ericmcdaniel/lumenlab/board/images/lumenlab-mounting-bracket-2.png

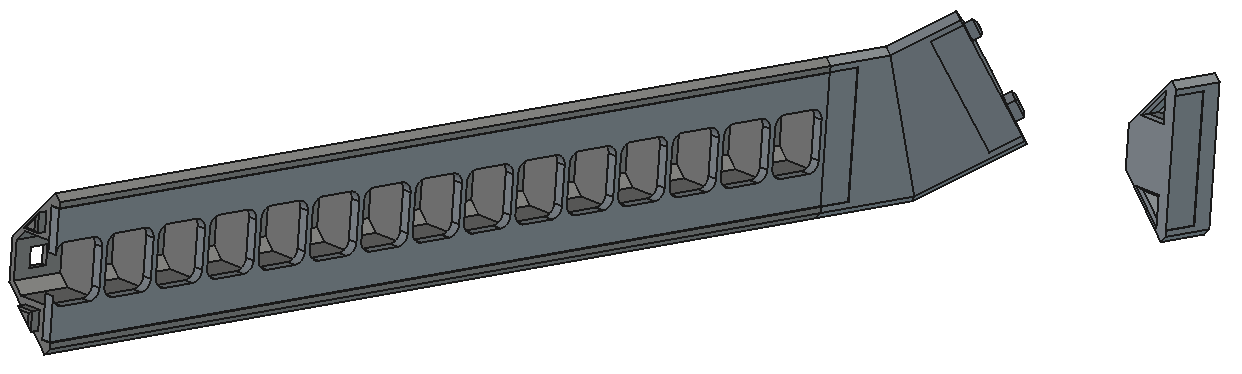
board/images/lumenlab-mounting-bracket-2.png
