ericmcdaniel/lumenlab/board/3d-models/0ZRE0005FF1C.stp

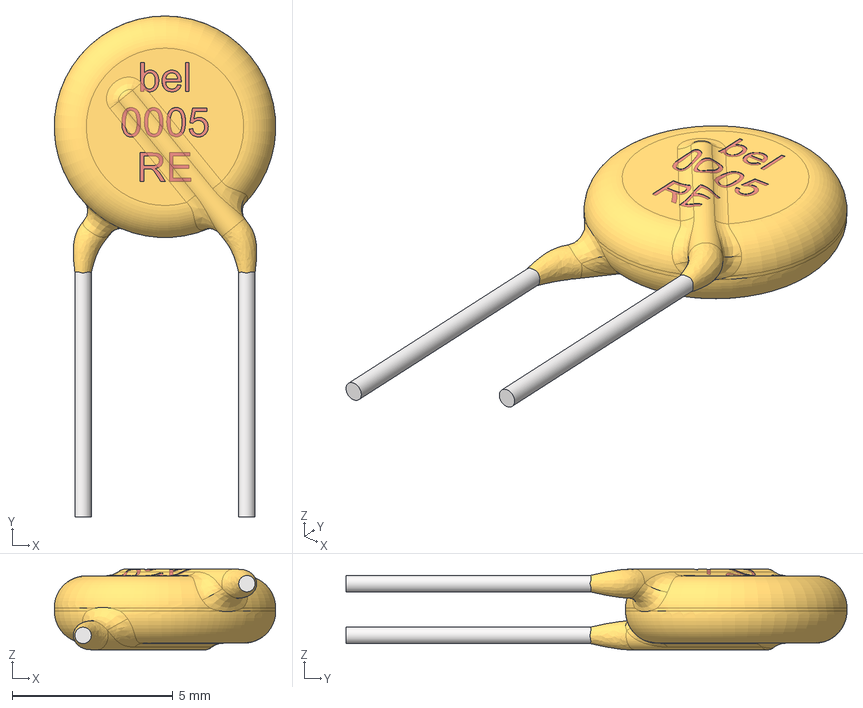
[picture p35: CAD file, 2025-10-11]
board/3d-models/0ZRE0005FF1C.stp
6.90 x 15.6 x 2.52 mm
0ZRE0005FF1C_PART1
0ZRE0005FF1C_PART2
0ZRE0005FF1C_PART3
0ZRE0005FF1C_PART4
