ericmcdaniel/lumenlab/board/mount/v3/led-strip-v3-bracket-only-mounting-guide.3mf

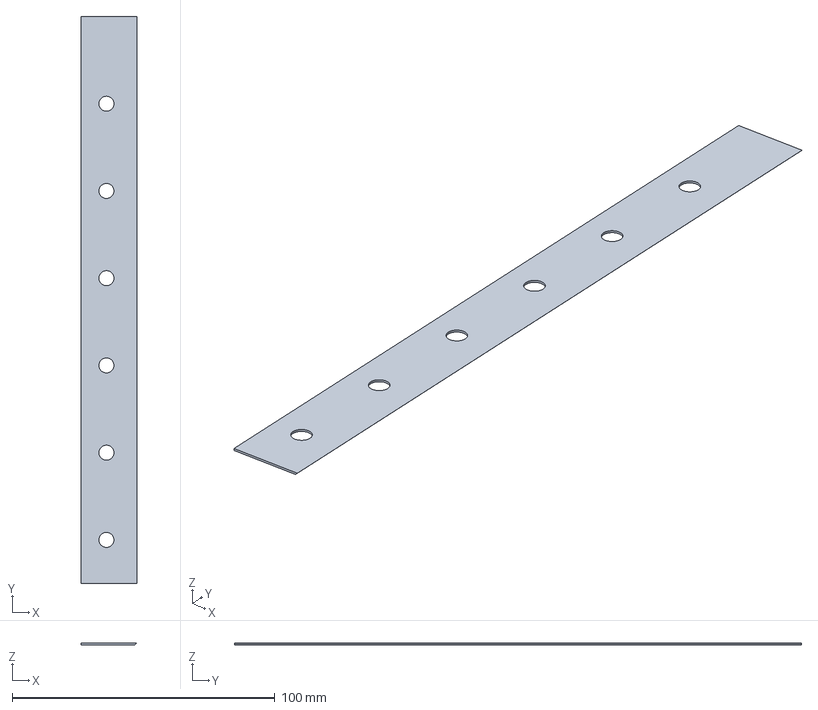
[picture p36: CAD file, 2026-06-20]
board/mount/v3/led-strip-v3-bracket-only-mounting-guide.3mf
21.1 x 215.7 x 0.604 mm
