ericmcdaniel/lumenlab/board/3d-models/CP2102N-A02-GQFN24R.step

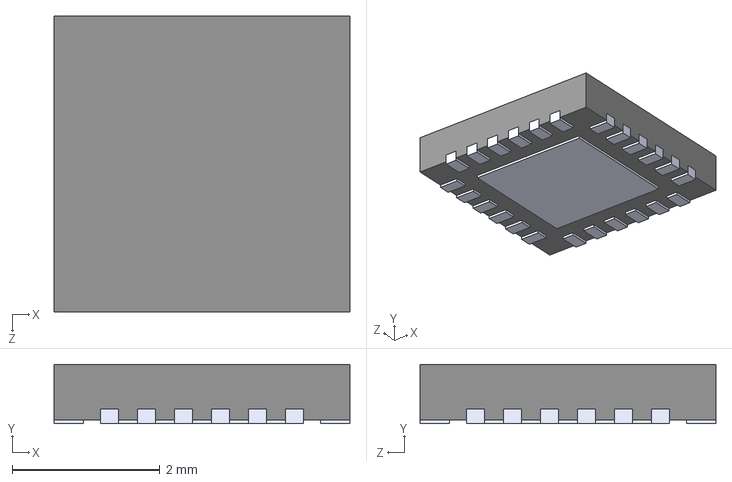
[picture p37: CAD file, 2025-10-11]
board/3d-models/CP2102N-A02-GQFN24R.step
4.00 x 0.8 x 4.00 mm
