ericmcdaniel/lumenlab/board/3d-models/ESD122DMYR.step

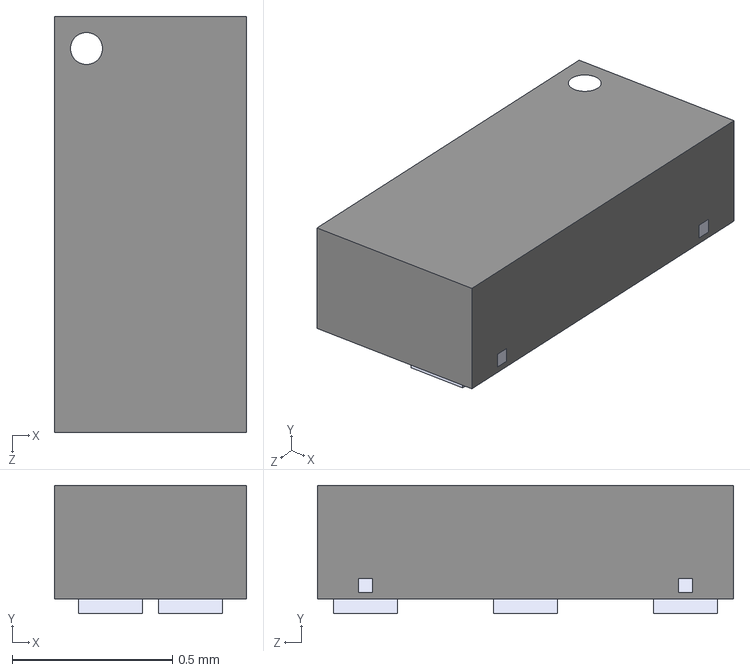
[picture p38: CAD file, 2025-10-11]
board/3d-models/ESD122DMYR.step
0.6 x 0.4 x 1.30 mm
