ericmcdaniel/lumenlab/board/mount/v3/plywood-retention-clip.3mf

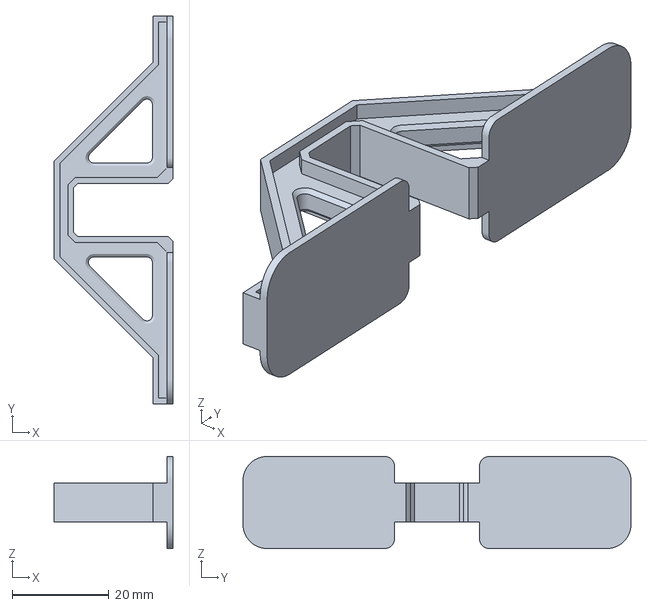
[picture p39: CAD file, 2026-05-21]
board/mount/v3/plywood-retention-clip.3mf
24.5 x 80.0 x 19.0 mm
