ericmcdaniel/lumenlab/board/3d-models/B4PS-VH-jst-vh-connector.step

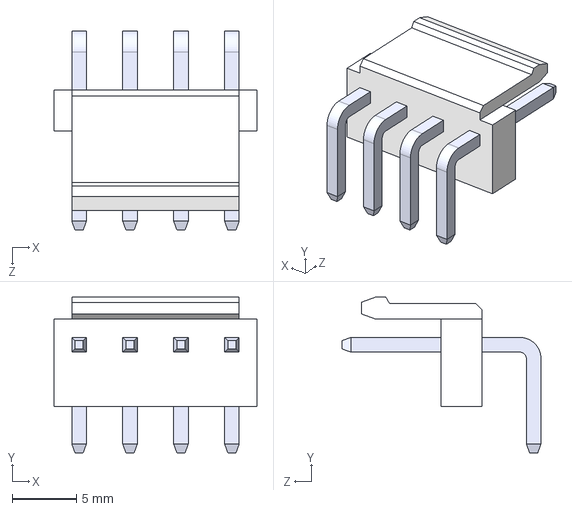
[picture p40: CAD file, 2025-10-11]
board/3d-models/B4PS-VH-jst-vh-connector.step
15.8 x 12.1 x 15.5 mm
BxPS-VH_4
pin^BxPS-VH ass x 4
