ericmcdaniel/lumenlab/board/mount/v3/led-strip-v3-bracket-only.3mf

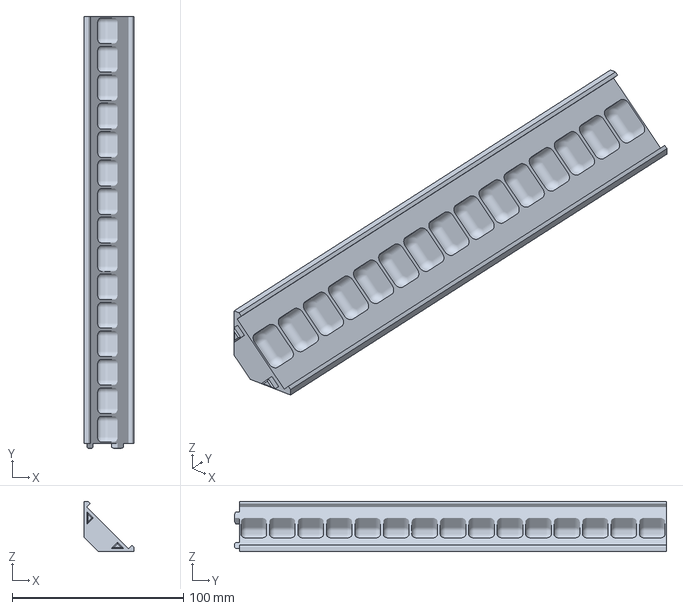
[picture p41: CAD file, 2026-04-02]
board/mount/v3/led-strip-v3-bracket-only.3mf
29.2 x 252.4 x 29.2 mm
