ericmcdaniel/lumenlab/board/3d-models/EMZS250ARA102MJA0G-led-decoupling-cap.step

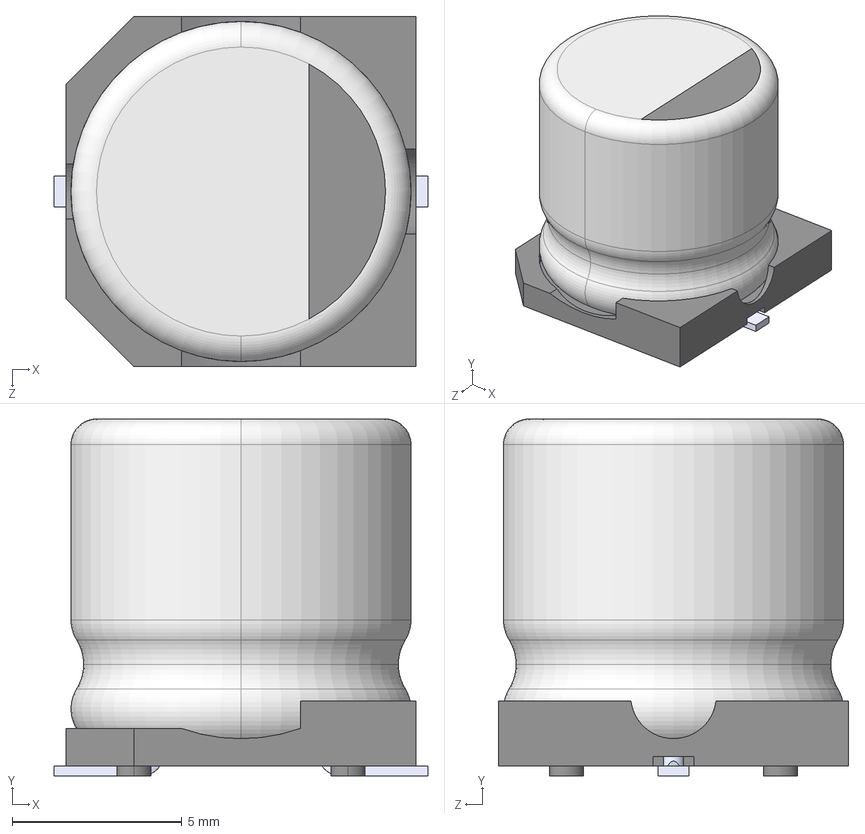
[picture p42: CAD file, 2025-10-11]
board/3d-models/EMZS250ARA102MJA0G-led-decoupling-cap.step
11.0 x 10.5 x 10.3 mm
