ericmcdaniel/lumenlab/board/mount/v3/led-strip-v3-bracket-mirrored.3mf

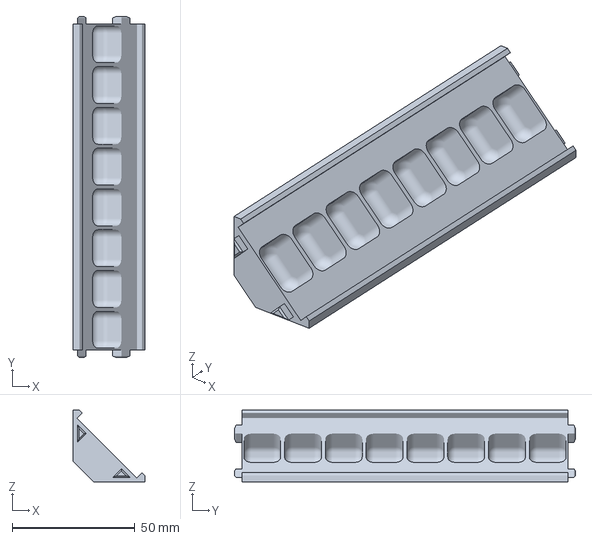
[picture p43: CAD file, 2026-04-02]
board/mount/v3/led-strip-v3-bracket-mirrored.3mf
29.2 x 139.0 x 29.2 mm
