ericmcdaniel/lumenlab/board/3d-models/USB-C.step

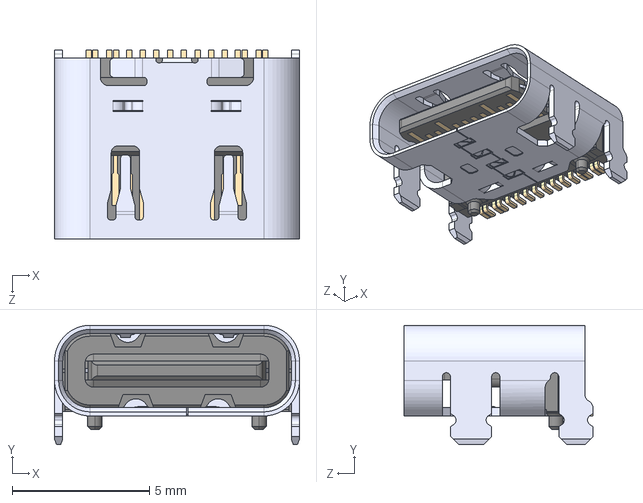
[picture p44: CAD file, 2025-10-11]
board/3d-models/USB-C.step
8.94 x 4.36 x 6.90 mm
