ericmcdaniel/lumenlab/board/mount/v3/led-strip-v3-bracket-w-endcap.3mf

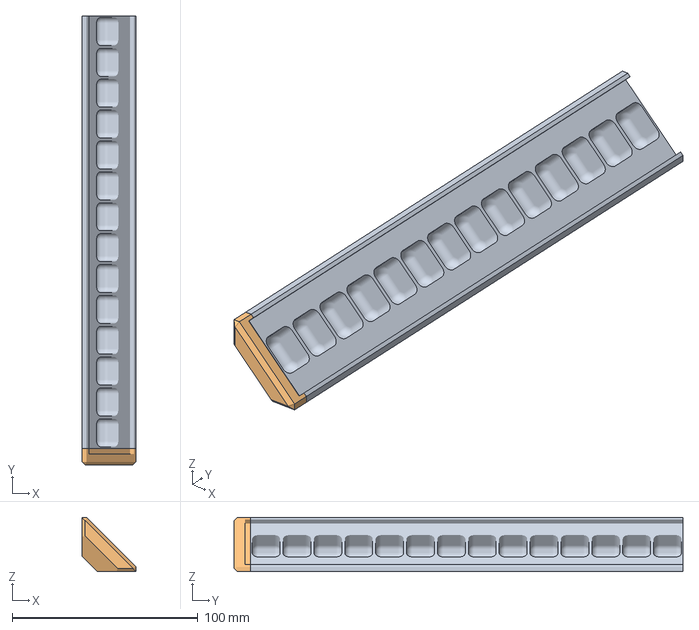
[picture p45: CAD file, 2026-04-02]
board/mount/v3/led-strip-v3-bracket-w-endcap.3mf
29.2 x 241.8 x 29.2 mm
