ericmcdaniel/lumenlab/board/3d-models/potentiometer.step

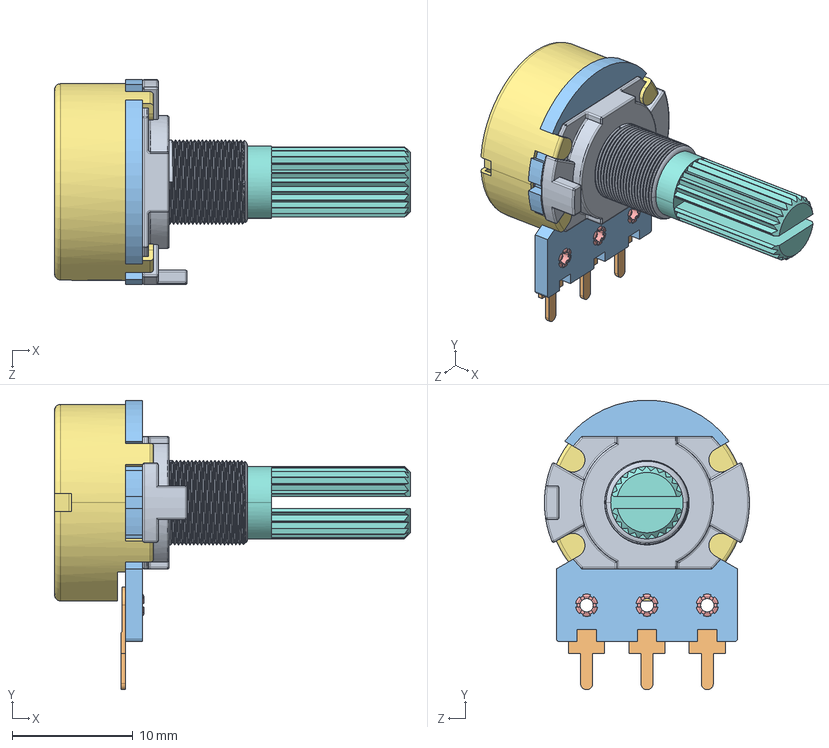
[picture p46: CAD file, 2025-10-01]
board/3d-models/potentiometer.step
29.5 x 24.0 x 17.0 mm
PTN16_1 BUSHING
PTN16-A_1 HOUSING
PTN16_20K1_SHAFT
