ericmcdaniel/lumenlab/board/mount/v3/led-strip-v3-bracket-w-45deg-joint.3mf

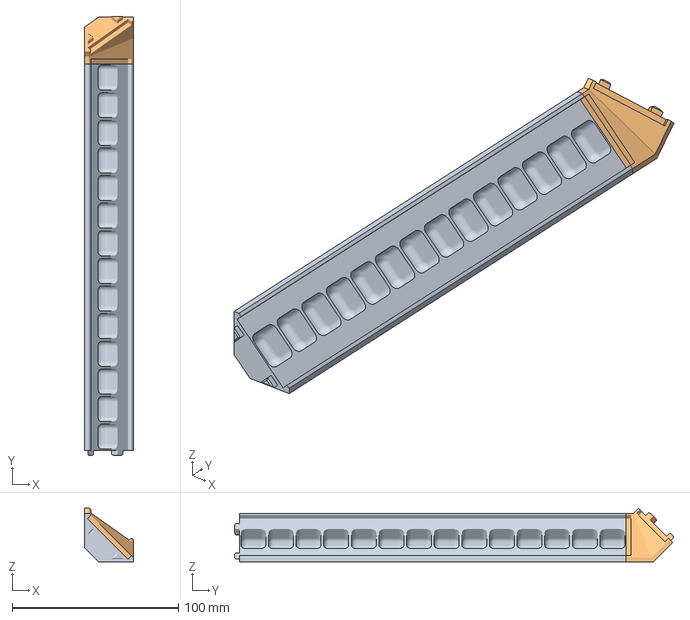
[picture p47: CAD file, 2026-04-02]
board/mount/v3/led-strip-v3-bracket-w-45deg-joint.3mf
29.3 x 264.3 x 32.3 mm
