ericmcdaniel/lumenlab/board/3d-models/BarrelJack.step

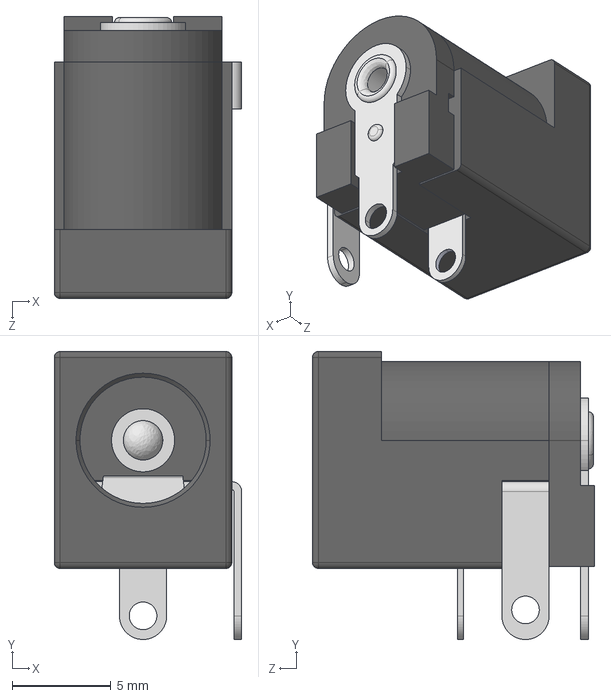
[picture p48: CAD file, 2025-10-01]
board/3d-models/BarrelJack.step
9.50 x 14.6 x 14.3 mm
