ericmcdaniel/lumenlab/board/3d-models/SSD1306.step

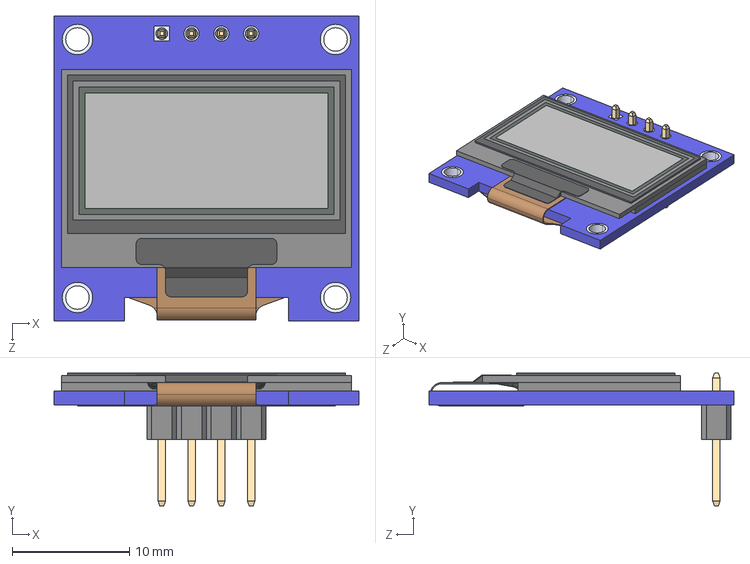
[picture p49: CAD file, 2025-10-01]
board/3d-models/SSD1306.step
26.0 x 11.3 x 26.0 mm
DM-OLED096-636_Module
DM-OLED096-636_Panel
