ericmcdaniel/lumenlab/board/3d-models/1264EY-6R8M_P3-inductor.step

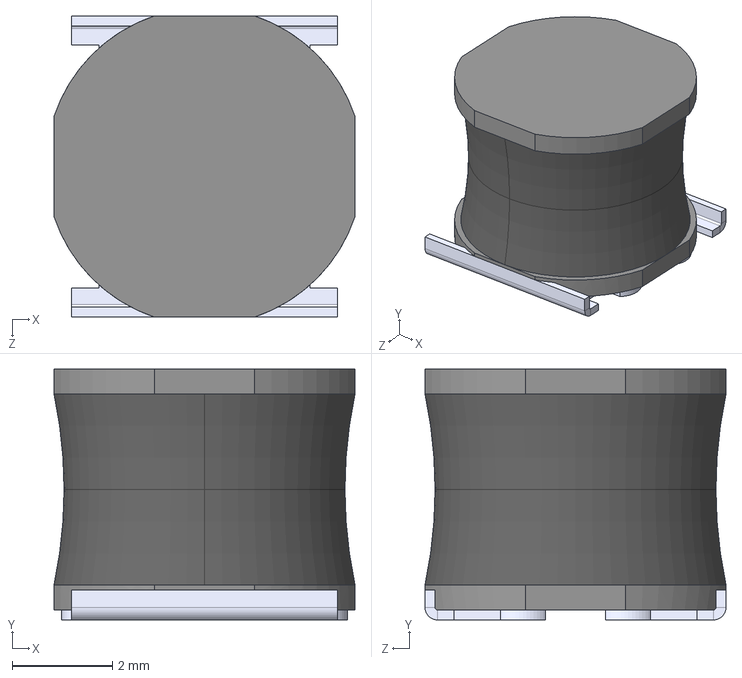
[picture p50: CAD file, 2025-10-01]
board/3d-models/1264EY-6R8M_P3-inductor.step
6.00 x 5.00 x 6.00 mm
