ericmcdaniel/lumenlab/board/3d-models/504-nav-switch.stp

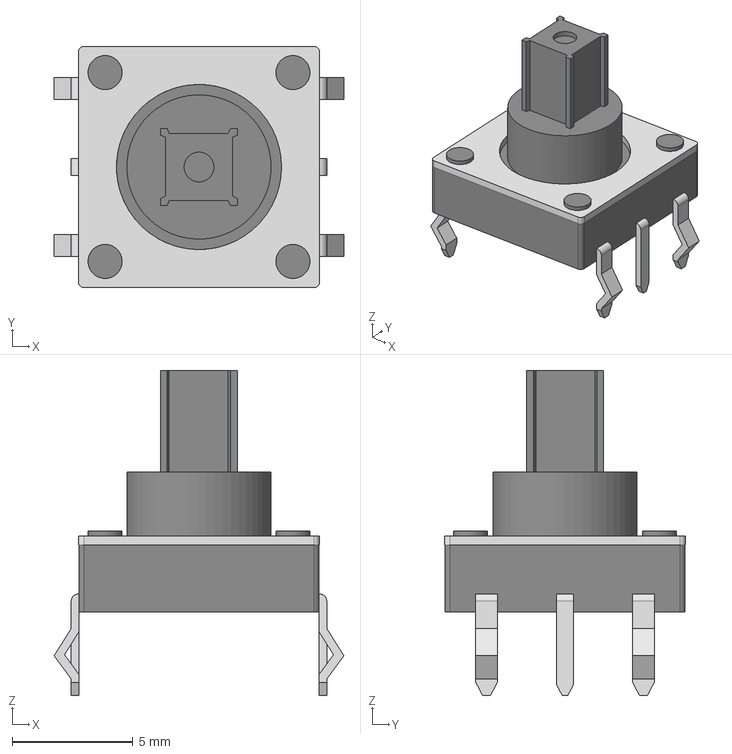
[picture p51: CAD file, 2025-10-01]
board/3d-models/504-nav-switch.stp
12.0 x 10.0 x 13.5 mm
