ericmcdaniel/lumenlab/board/3d-models/B2B-PH-K-S.step

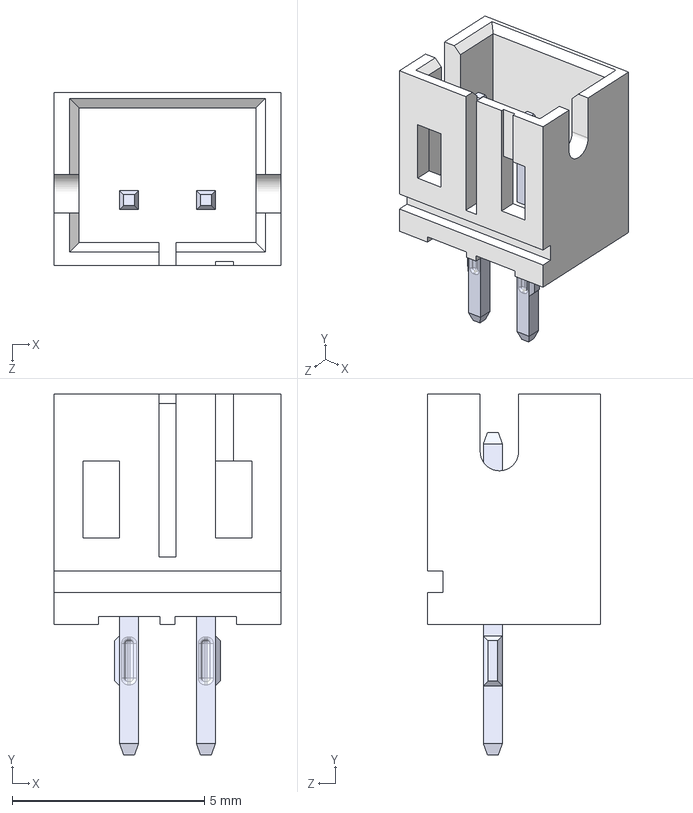
[picture p52: CAD file, 2025-10-01]
board/3d-models/B2B-PH-K-S.step
5.90 x 9.40 x 4.50 mm
