ericmcdaniel/lumenlab/board/3d-models/16SEPF1000M.step

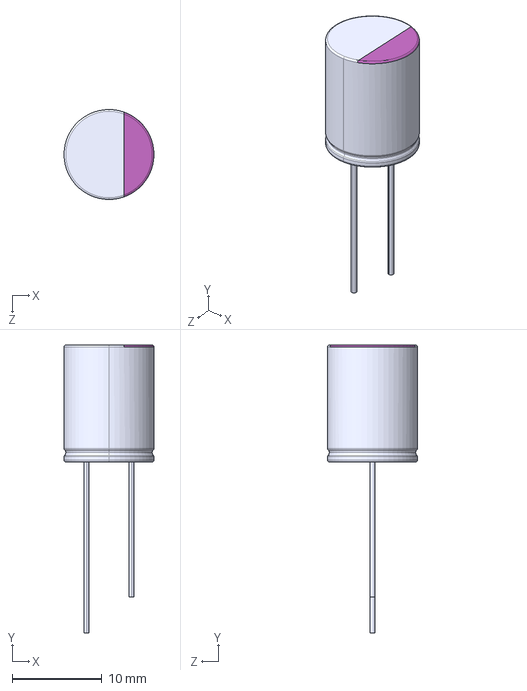
[picture p53: CAD file, 2025-10-01]
board/3d-models/16SEPF1000M.step
10.0 x 32.0 x 10.0 mm
