ericmcdaniel/lumenlab/board/3d-models/SMAJ12CA-tvs-diode.step

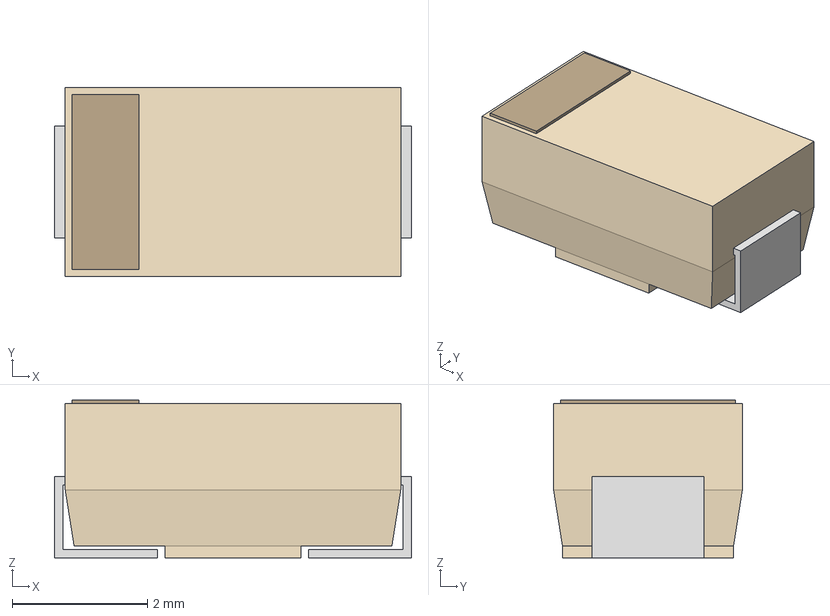
[picture p54: CAD file, 2025-10-01]
board/3d-models/SMAJ12CA-tvs-diode.step
5.28 x 2.79 x 2.34 mm
