ericmcdaniel/lumenlab/board/3d-models/10TZV220M6-speaker-cap.step

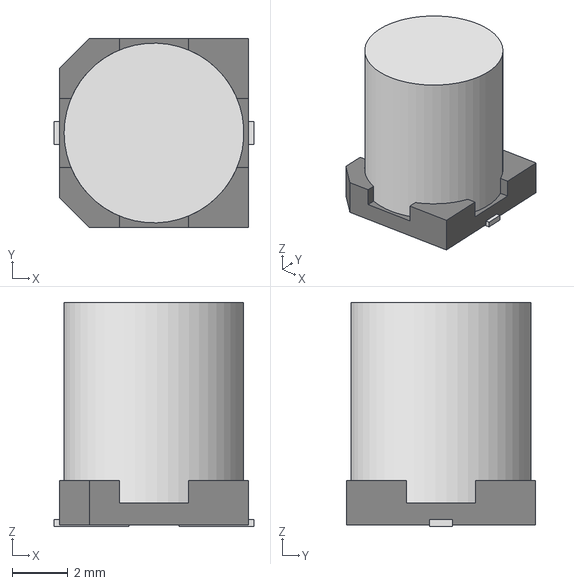
[picture p55: CAD file, 2025-10-01]
board/3d-models/10TZV220M6-speaker-cap.step
7.19 x 6.81 x 8.05 mm
