ericmcdaniel/lumenlab/board/3d-models/JTAG-header.STEP

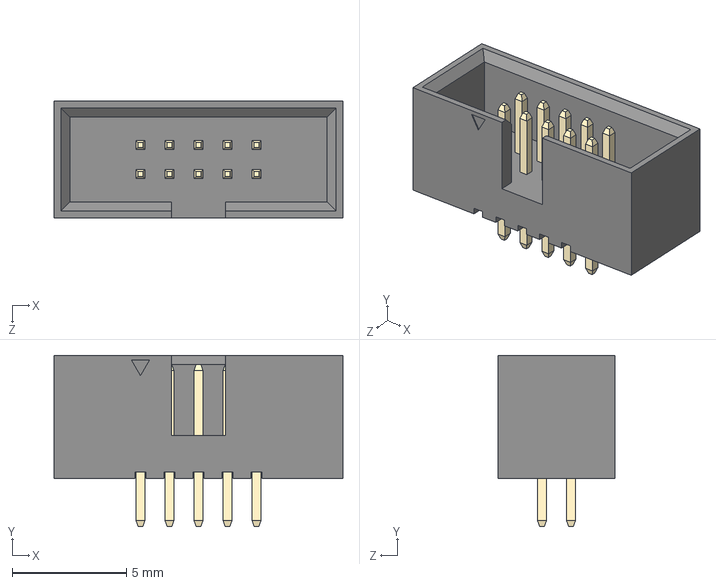
[picture p56: CAD file, 2025-10-01]
board/3d-models/JTAG-header.STEP
12.7 x 7.50 x 5.10 mm
3220-xx-0100-00 body_10
Pin^3220-xx-0100-00 x 10
