ericmcdaniel/lumenlab/board/3d-models/FTSH-105-01-S-DV-TR.step

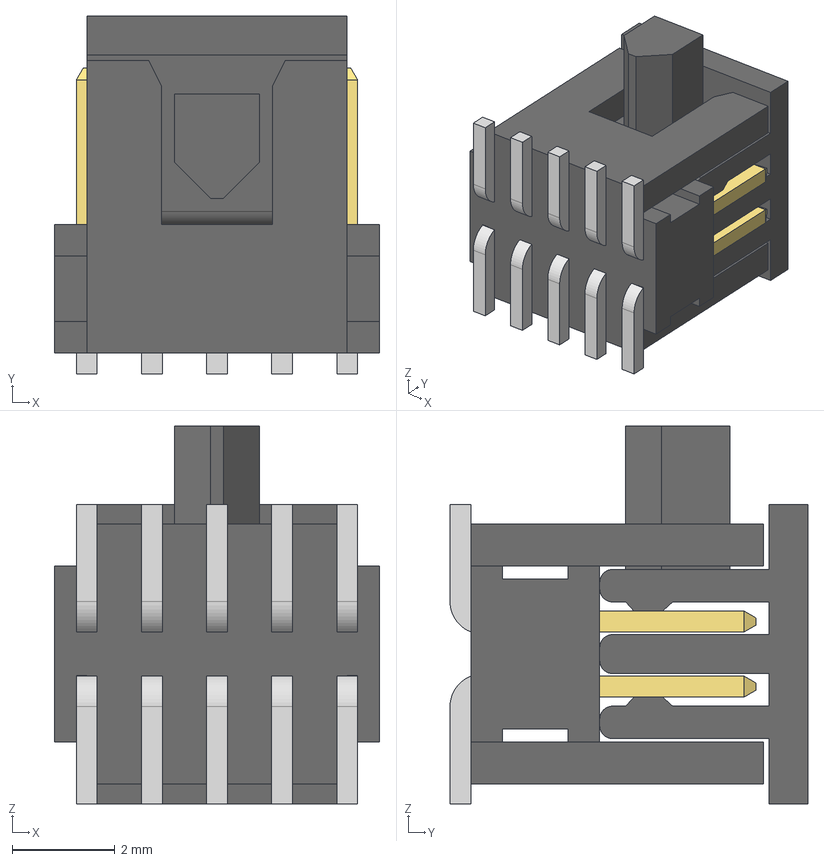
[picture p57: CAD file, 2025-10-01]
board/3d-models/FTSH-105-01-S-DV-TR.step
6.35 x 6.98 x 7.37 mm
FTSH-105-01-S-DV-K-P-TR_body
FTSH-105-01-S-DV-K-P-TR_pins1
FTSH-105-01-S-DV-K-P-TR_pins2
FTSH-105-01-S-DV-K-P-TR_pp_pad
