ericmcdaniel/lumenlab/board/3d-models/SN74HC14DR.step

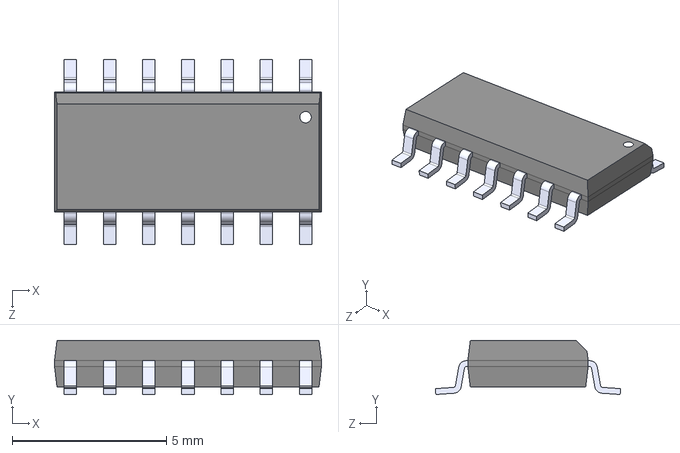
[picture p58: CAD file, 2025-09-19]
board/3d-models/SN74HC14DR.step
8.65 x 1.75 x 6.00 mm
