ericmcdaniel/lumenlab/board/3d-models/LM386MX-1_NOPB.step

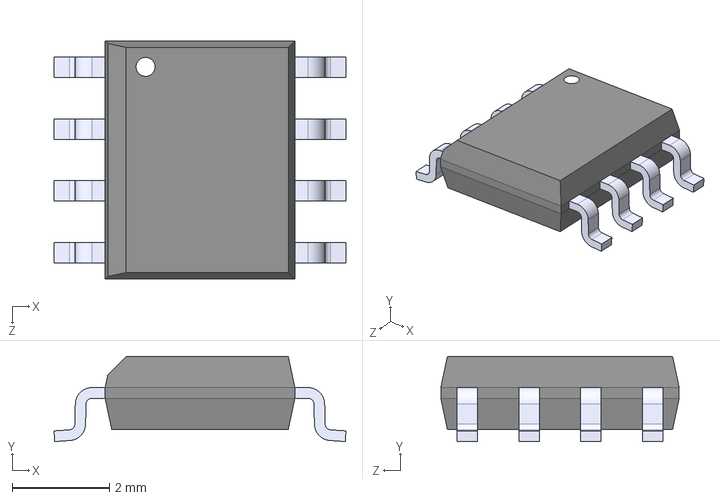
[picture p59: CAD file, 2025-09-19]
board/3d-models/LM386MX-1_NOPB.step
6.00 x 1.75 x 4.90 mm
