ericmcdaniel/lumenlab/board/3d-models/SN74AHCT1G125DBVR.step

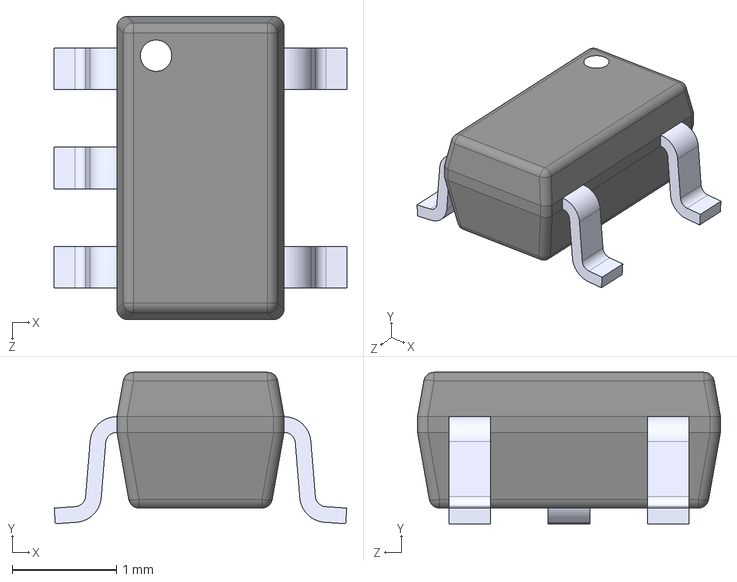
[picture p60: CAD file, 2025-09-19]
board/3d-models/SN74AHCT1G125DBVR.step
2.80 x 1.45 x 2.90 mm
