ericmcdaniel/lumenlab/board/3d-models/MP2338.step

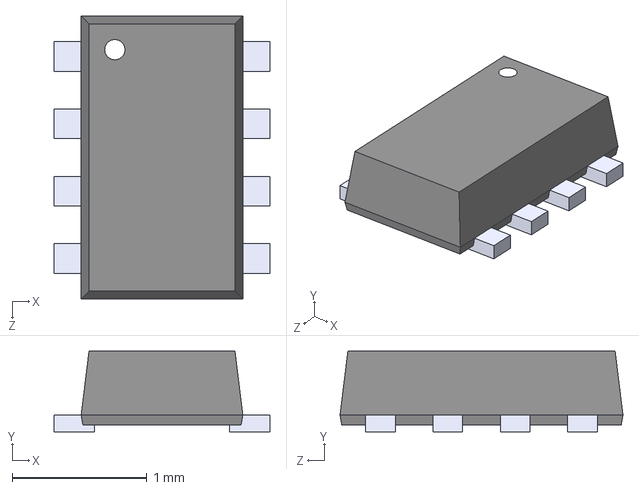
[picture p61: CAD file, 2025-09-19]
board/3d-models/MP2338.step
1.60 x 0.6 x 2.10 mm
