ericmcdaniel/lumenlab/src/display/display.cpp

#include <Wire.h>
#include <cstdarg>

#include "display/display.h"
#include "core/context-manager.h"

namespace Display
{
  OledDisplay::OledDisplay(SystemCore::ContextManager *ctx) : contextManager{ctx}
  {
    Wire.begin();
    display.begin(SSD1306_SWITCHCAPVCC, DISPLAY_ADDRESS);
    display.setTextColor(SSD1306_WHITE);
    display.setTextSize(1);
    drawBootScreen();
  }

  void OledDisplay::updateDisplay()
  {
    Engine::StateManager &state = contextManager->stateManager;
    if (!state.displayIsVisible && state.displayShouldUpdate)
    {
      clearDisplay();
      state.displayShouldUpdate = false;
      return;
    }

    if (state.displayShouldUpdate)
    {
      switch (state.current())
      {
      case Engine::SystemState::Initialize:
        drawBootScreen();
        break;
      case Engine::SystemState::MenuHome:
        drawMainMenu();
        break;
      case Engine::SystemState::MenuGames:
        drawGamesMenu();
        break;
      case Engine::SystemState::MenuScenes:
        drawScenesMenu();
        break;
      case Engine::SystemState::GameDemo:
        drawDemoGameHud();
        break;
      case Engine::SystemState::GameRecall:
        drawRecallGameHud();
        break;
      case Engine::SystemState::GamePhaseEvasion:
        drawPhaseEvasionGameHud();
        break;
      case Engine::SystemState::GameChainReaction:
        drawChainReactionGameHud();
        break;
      case Engine::SystemState::GameReflex:
        drawReflexGameHud();
        break;
      case Engine::SystemState::SceneCanvas:
        drawCanvasSceneHud();
        break;
      case Engine::SystemState::NoControllerConnected:
        drawUnconnectedControllerScreen();
        break;
      default:
        drawBootScreen();
        break;
      }
      state.displayShouldUpdate = false;
    }
  }

  int16_t OledDisplay::calculateCenterText(const char *text)
  {
    // unitialized but mutated by the Adafruit library
    int16_t textStartX, textStartY;
    uint16_t textWidth, textHeight;

    display.getTextBounds(text, 0, 0, &textStartX, &textStartY, &textWidth, &textHeight);

    int16_t centeredX = (DISPLAY_WIDTH - textWidth) / 2;
    return centeredX;
  }

  void OledDisplay::drawHeader(const char *message)
  {
    auto startingX = calculateCenterText(message);
    display.setCursor(startingX, 0);
    display.print(message);
  }

  void OledDisplay::debugUpdateDisplay(const char *format, ...)
  {
#ifdef VIRTUALIZATION
    char oledBuffer[256] = "";
    va_list args;
    va_start(args, format);
    vsnprintf(oledBuffer, sizeof(oledBuffer), format, args);
    va_end(args);
    Display::sendOledUpdate(oledBuffer);
#endif
  }

  void OledDisplay::drawBootScreen()
  {
    display.clearDisplay();

    drawHeader("LumenLab");

    display.drawBitmap(initLogo.xPos, initLogo.yPos, initLogo.rawValues, initLogo.width, initLogo.height, SSD1306_WHITE);
    display.display();
  }

  void OledDisplay::clearDisplay()
  {
    display.clearDisplay();
    display.display();
  }

  void OledDisplay::drawMainMenu()
  {
    display.clearDisplay();
    drawHeader("Main Menu");

    uint8_t selectedOptionIndex = static_cast<uint8_t>(contextManager->stateManager.getUserMenuChoice());

    display.setCursor(0, 8);
    display.print(selectedOption(0, selectedOptionIndex));
    display.print("  Games");
    display.setCursor(0, 16);
    display.print(selectedOption(1, selectedOptionIndex));
    display.print("  Scenes");

    debugUpdateDisplay("   Main Menu\n%c  Games\n%c  Scenes",
                       selectedOption(0, selectedOptionIndex), selectedOption(1, selectedOptionIndex));

    display.display();
  }

  void OledDisplay::drawGamesMenu()
  {
    constexpr int itemsPerPage = 3;
    constexpr int numGames = static_cast<int>(Engine::GameSelection::COUNT);
    uint8_t selectedOptionIndex = static_cast<uint8_t>(contextManager->stateManager.getUserGameChoice());
    auto currentPage = selectedOptionIndex / itemsPerPage;
    char nameBuffer[32] = "";

    display.clearDisplay();
    sprintf(nameBuffer, "Games Menu (%d/%d)", currentPage + 1, (numGames + itemsPerPage - 1) / itemsPerPage);
    drawHeader(nameBuffer);

    int startIndex = currentPage * itemsPerPage;
    int endIndex = std::min(startIndex + itemsPerPage, numGames);

    for (int i = startIndex; i < endIndex; ++i)
    {
      display.setCursor(0, 8 * (i - startIndex + 1));
      sprintf(nameBuffer, "%c  %s", selectedOption(i, selectedOptionIndex), contextManager->stateManager.printGameName(i));
      display.print(nameBuffer);
    }

    char oledBuffer[256] = "";
    int offset = snprintf(oledBuffer, sizeof(oledBuffer), "Games Menu (%d/%d)", currentPage + 1, (numGames + itemsPerPage - 1) / itemsPerPage);
    for (int i = startIndex; i < endIndex; ++i)
    {
      offset += snprintf(oledBuffer + offset, sizeof(oledBuffer) - offset, "\n%c  %s",
                         selectedOption(i, selectedOptionIndex), contextManager->stateManager.printGameName(i));
    }
    debugUpdateDisplay("%s", oledBuffer);

    display.display();
  }

  void OledDisplay::drawScenesMenu()
  {
    display.clearDisplay();
    drawHeader("Scenes Menu");

    uint8_t selectedOptionIndex = static_cast<uint8_t>(contextManager->stateManager.getUserSceneChoice());
    char nameBuffer[32] = "";

    display.setCursor(0, 8);
    sprintf(nameBuffer, "%c  %s", selectedOption(0, selectedOptionIndex), contextManager->stateManager.printSceneName(0));
    display.print(nameBuffer);

    debugUpdateDisplay("     Scenes Menu\n%c  %s",
                       selectedOption(0, selectedOptionIndex), contextManager->stateManager.printSceneName(0));

    display.display();
  }

  void OledDisplay::drawDemoGameHud()
  {
    display.clearDisplay();
    drawHeader("Demo");

    display.setCursor(0, 16);
    display.print("Current Score: ");
    display.print(contextManager->stateManager.getDemoGameState().currentScore);
    display.setCursor(0, 24);
    display.print("High Score: -");

    debugUpdateDisplay("     Demo\nCurrent Score: %u\nHigh Score: -",
                       contextManager->stateManager.getDemoGameState().currentScore);

    display.display();
  }

  void OledDisplay::drawRecallGameHud()
  {
    const auto recallState = contextManager->stateManager.getRecallGameState();
    const auto round = recallState.round;
    const auto highScore = recallState.highScore;

    display.clearDisplay();
    drawHeader("Recall");

    display.setCursor(0, 16);
    display.printf("Round: %u", round + 1);
    display.setCursor(0, 24);
    display.printf("High Score: %u", highScore + 1);

    debugUpdateDisplay("     Recall\nRound: %u\nHigh Score: %u", round + 1, highScore + 1);

    display.display();
  }

  void OledDisplay::drawPhaseEvasionGameHud()
  {
    const auto phaseEvasionState = contextManager->stateManager.getPhaseEvasionGameState();
    const auto flaresEvaded = phaseEvasionState.flaresEvaded;
    const auto gemsCaptured = phaseEvasionState.gemsCaptured;
    const auto totalScore = phaseEvasionState.calculateTotalScore();
    const auto highScore = phaseEvasionState.highScore;

    display.clearDisplay();
    drawHeader("Phase Evasion");

    display.setCursor(0, 16);
    display.printf("Flares: %u", flaresEvaded);
    display.setCursor(DISPLAY_WIDTH / 2 + 4, 16);
    display.printf("Total: %u", totalScore);

    display.setCursor(0, 24);
    display.printf("  Gems: %u", gemsCaptured);
    display.setCursor(DISPLAY_WIDTH / 2 + 4, 24);
    display.printf(" High: %u", highScore);

    debugUpdateDisplay("     Phase Evasion\nFlares: %u   Total: %u\nGems: %u     High: %u",
                       flaresEvaded, totalScore, gemsCaptured, highScore);

    display.display();
  }

  void OledDisplay::drawChainReactionGameHud()
  {
    display.clearDisplay();
    drawHeader("Chain Reaction");

    const auto chainReactionState = contextManager->stateManager.getChainReactionGameState();
    const auto reactions = chainReactionState.reactions;

    display.setCursor(0, 16);
    display.printf("Reactions: %u", reactions);
    display.setCursor(0, 24);
    display.printf("Total: %u", reactions);

    debugUpdateDisplay("     Chain Reaction\nReactions: %u\nTotal: %u", reactions, reactions);

    display.display();
  }

  void OledDisplay::drawReflexGameHud()
  {
    display.clearDisplay();
    drawHeader("Reflex");

    const auto reflexState = contextManager->stateManager.getReflexGameState();

    debugUpdateDisplay("     Reflex");

    display.display();
  }

  void OledDisplay::drawCanvasSceneHud()
  {
    display.clearDisplay();
    drawHeader("Canvas");

    char colorBuffer[32] = "";
    auto &color = contextManager->stateManager.getCanvasSceneState().currentColor;
    sprintf(colorBuffer, "RGB: (%u, %u, %u)", color.r, color.g, color.b);
    display.setCursor(0, 24);
    display.print(colorBuffer);

    debugUpdateDisplay("     Canvas\nRGB: (%u, %u, %u)", color.r, color.g, color.b);

    display.display();
  }

  void OledDisplay::drawUnconnectedControllerScreen()
  {
    display.clearDisplay();
    drawHeader("LumenLab");

    char controllerTypeBuffer[32] = "";
    sprintf(controllerTypeBuffer, "%s controller", SystemCore::Configuration::psControllerType().c_str());

    auto startingX = calculateCenterText(controllerTypeBuffer);
    display.setCursor(startingX, 8);
    display.print(controllerTypeBuffer);

    startingX = calculateCenterText("not connected");
    display.setCursor(startingX, 16);
    display.print("not connected");

    debugUpdateDisplay("     LumenLab\n%s controller\nnot connected", SystemCore::Configuration::psControllerType().c_str());

    display.display();
  }
}
